wilyan09007/Tactus/data/analysis/exp/diag_registration_overlay.png

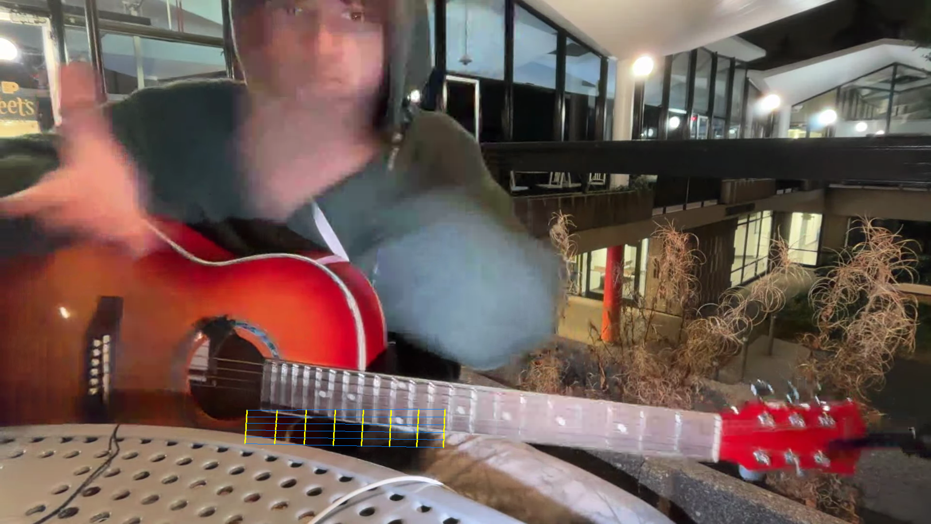
data/analysis/exp/diag_registration_overlay.png
