wilyan09007/Tactus/data/analysis/exp/e2_confusion.png

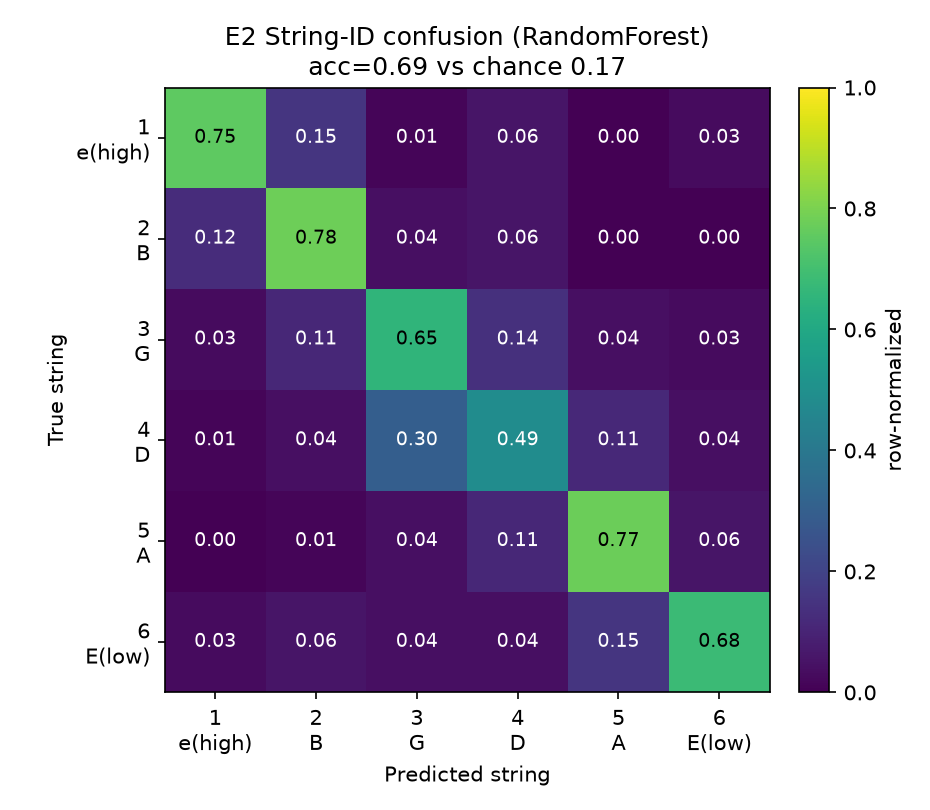
data/analysis/exp/e2_confusion.png
