wilyan09007/Tactus/data/analysis/exp/e3_transfer.png

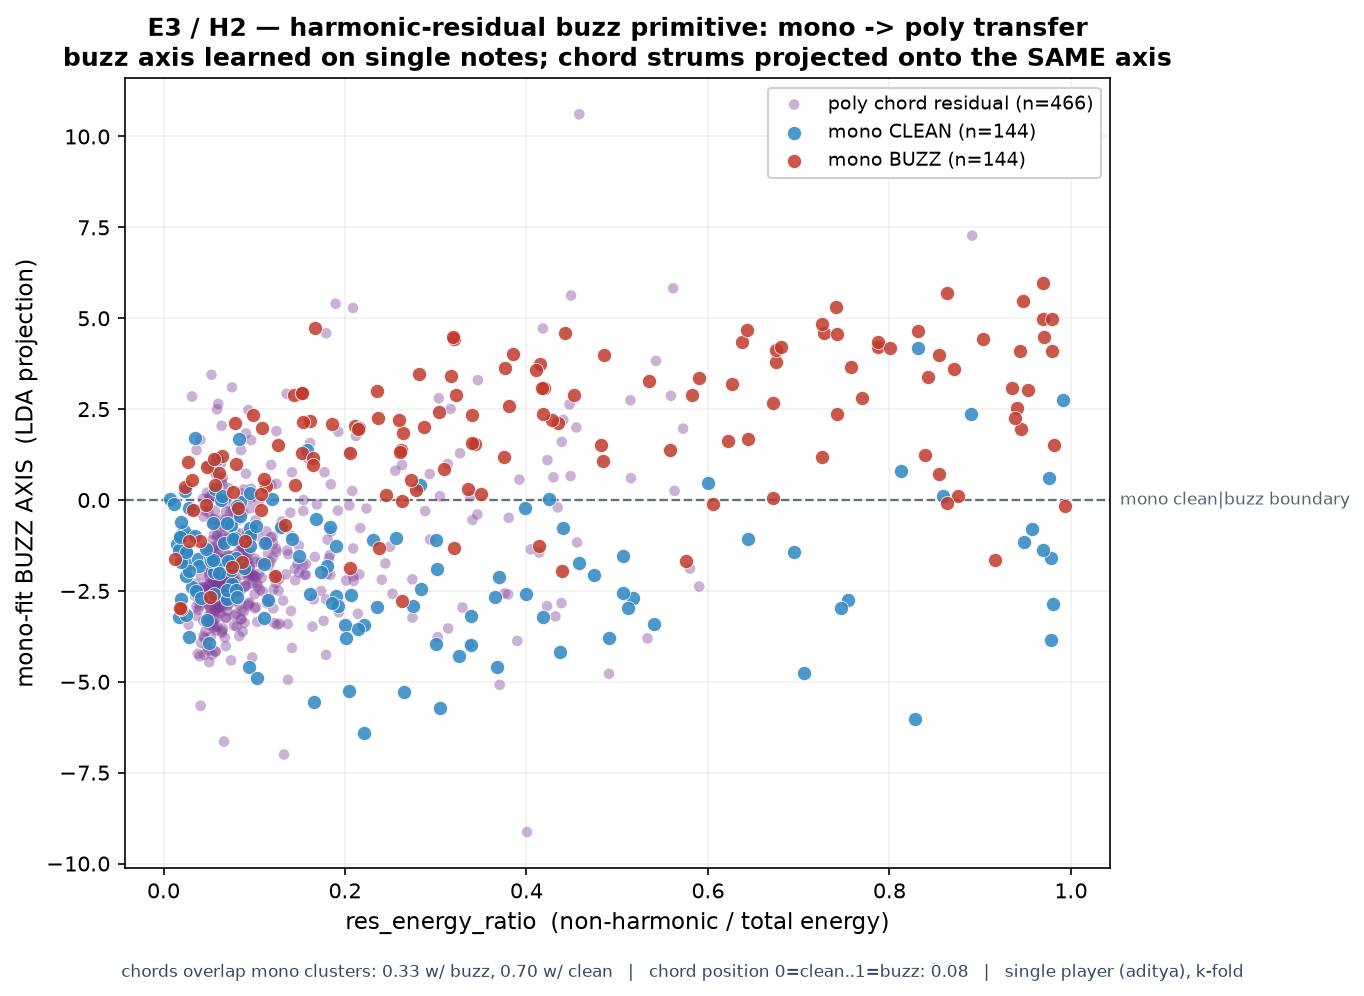
data/analysis/exp/e3_transfer.png
