wilyan09007/Tactus/data/analysis/exp/e4_chord_scatter.png

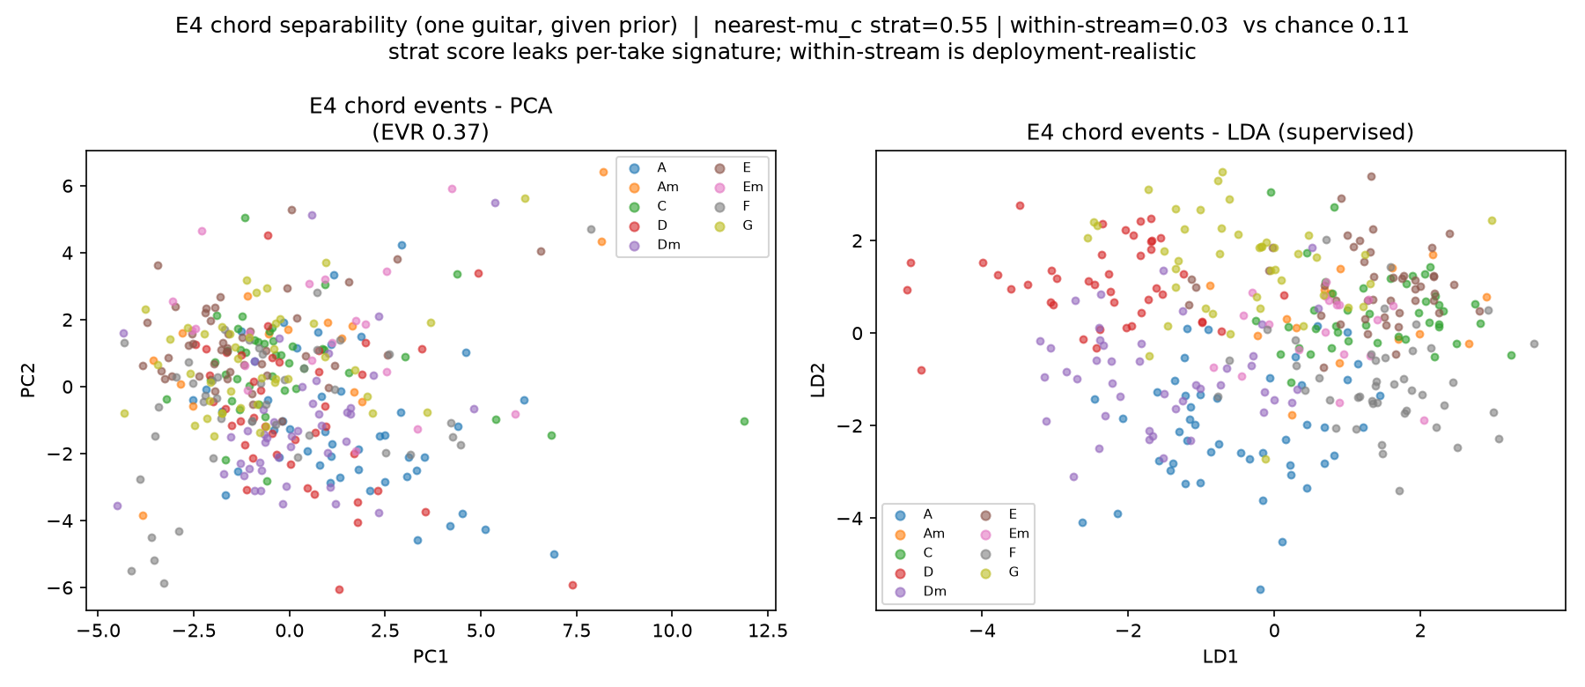
data/analysis/exp/e4_chord_scatter.png
