wilyan09007/Tactus/data/analysis/exp/e4_offdetect_roc.png

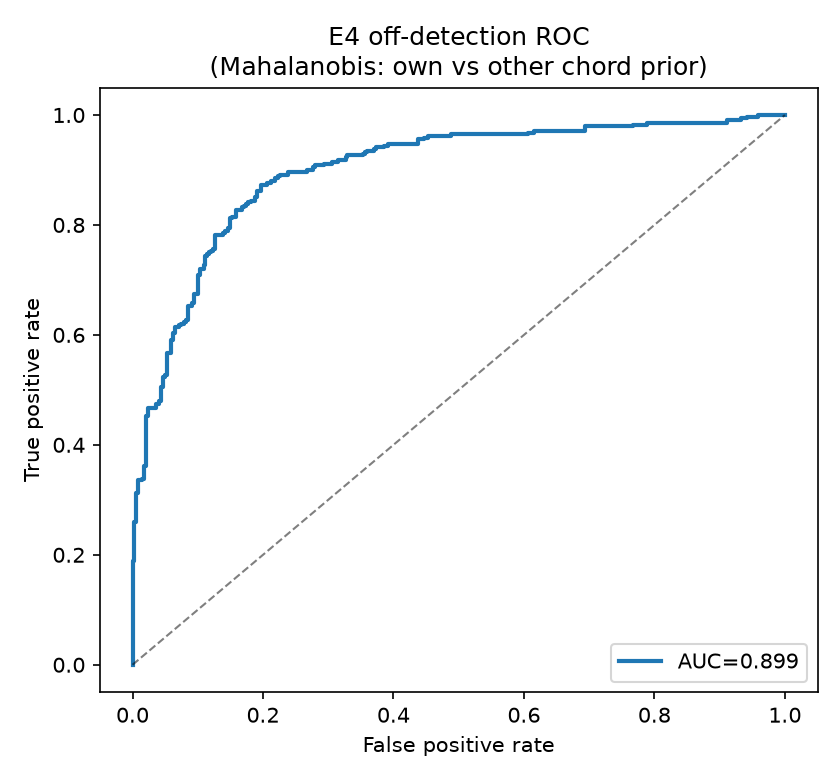
data/analysis/exp/e4_offdetect_roc.png
