wilyan09007/Tactus/data/analysis/exp/e5_harmonic_hist.png

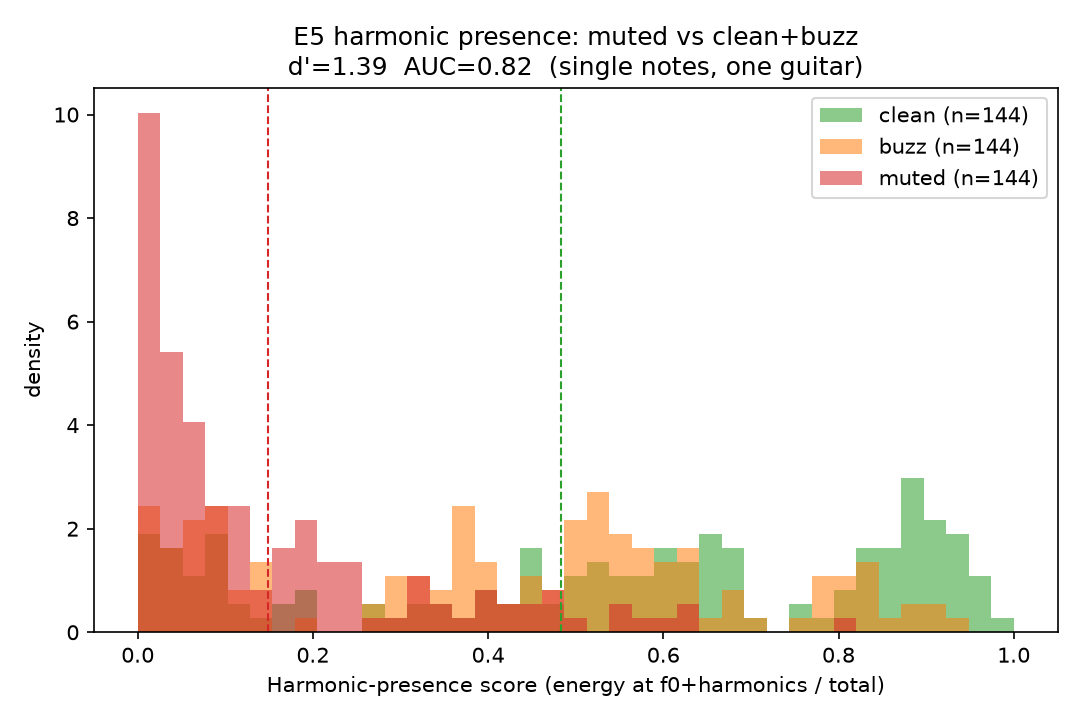
data/analysis/exp/e5_harmonic_hist.png
