wilyan09007/Tactus/data/analysis/exp/e5_harmonic_roc.png

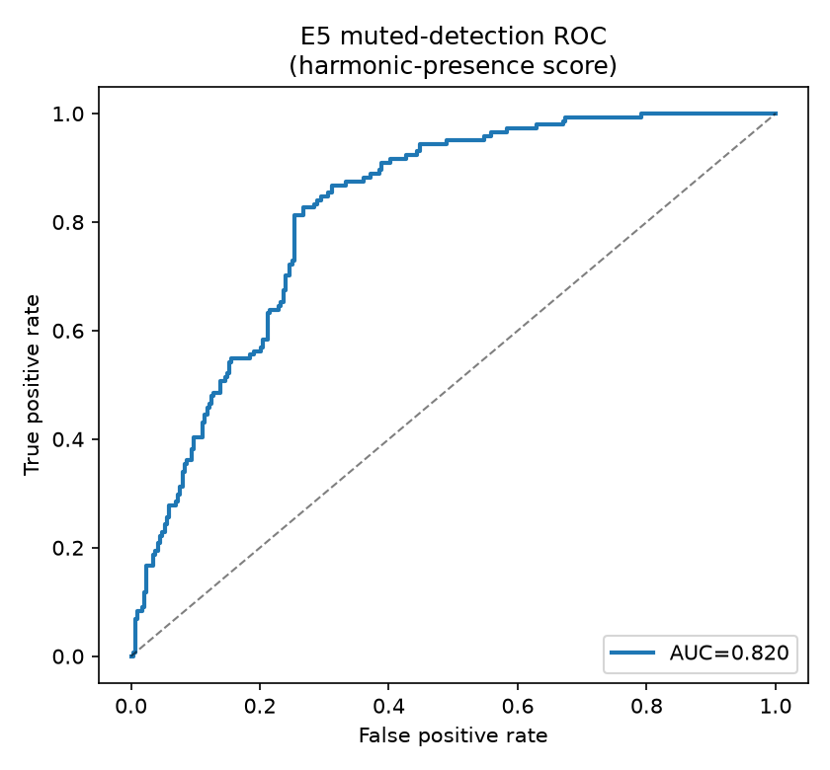
data/analysis/exp/e5_harmonic_roc.png
