wilyan09007/Tactus/data/analysis/exp/e7b_register_overlay.png

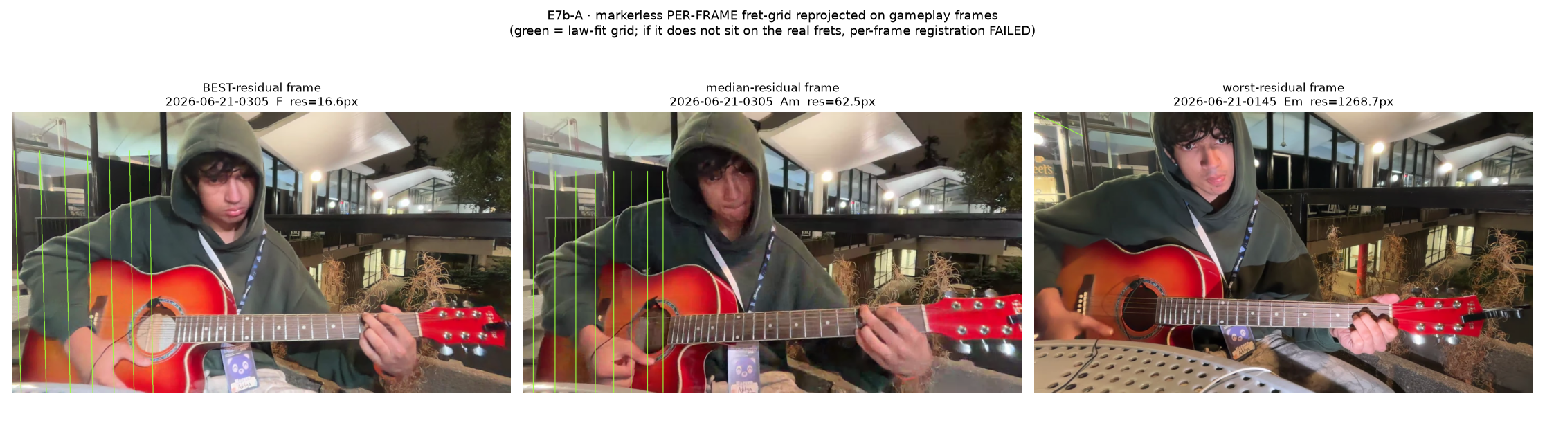
data/analysis/exp/e7b_register_overlay.png
