wilyan09007/Tactus/data/analysis/exp/e8_pose_chord_confusion.png

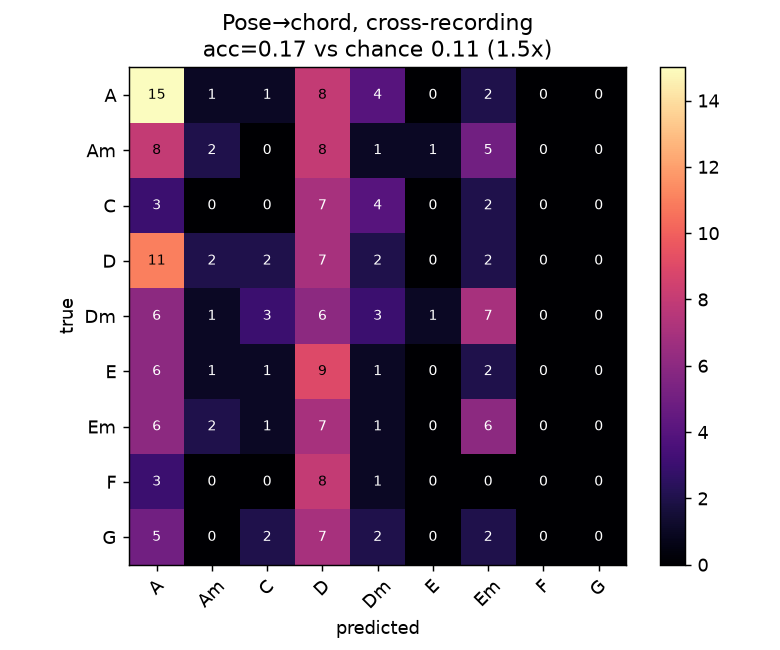
data/analysis/exp/e8_pose_chord_confusion.png
