wilyan09007/Tactus/data/analysis/exp/money_shot_fret_mae.png

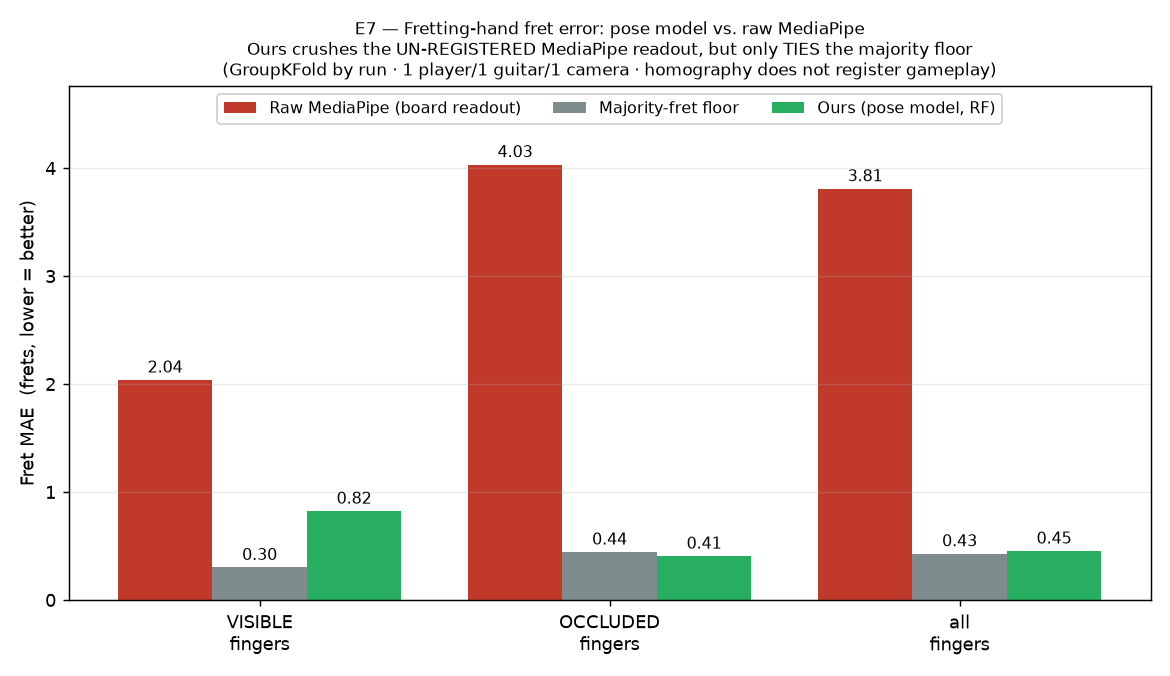
data/analysis/exp/money_shot_fret_mae.png
