wilyan09007/Tactus/data/analysis/exp/rotating_clusters.gif

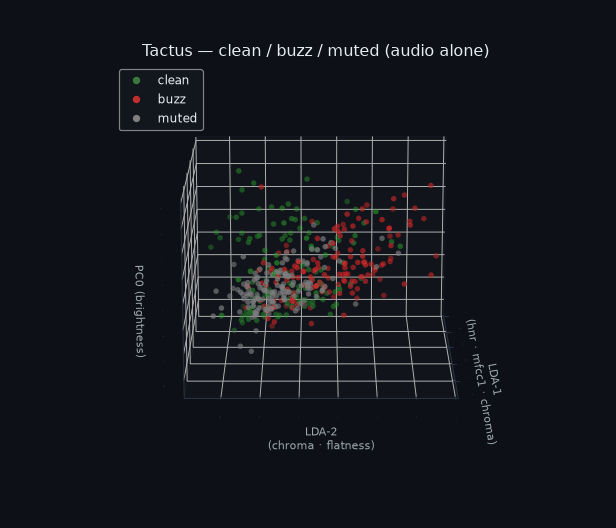
data/analysis/exp/rotating_clusters.gif
