wilyan09007/Tactus/data/analysis/exp/viz_clean_buzz_muted_3d.png

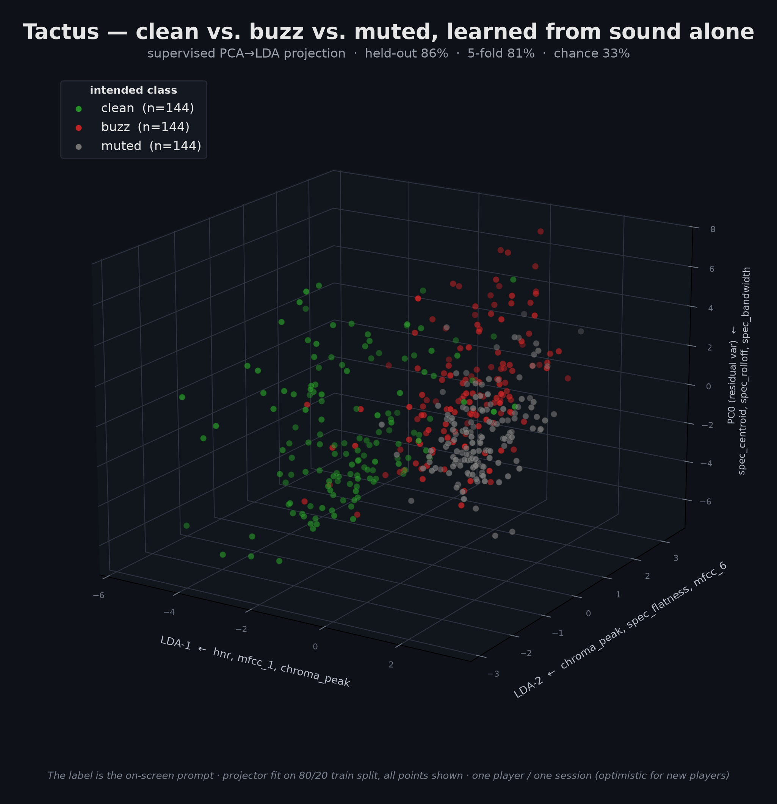
data/analysis/exp/viz_clean_buzz_muted_3d.png
