wilyan09007/Tactus/data/analysis/exp/viz_lda_2d.png

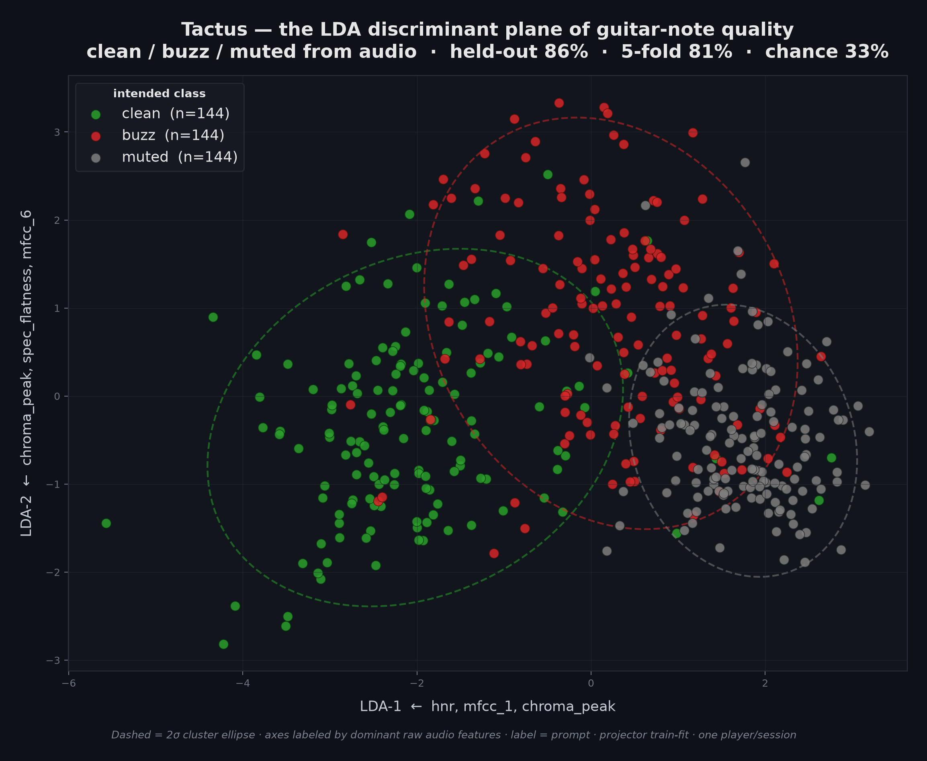
data/analysis/exp/viz_lda_2d.png
